scaleworkspace/covid19/Ventilator_Assembly/Plug.stl

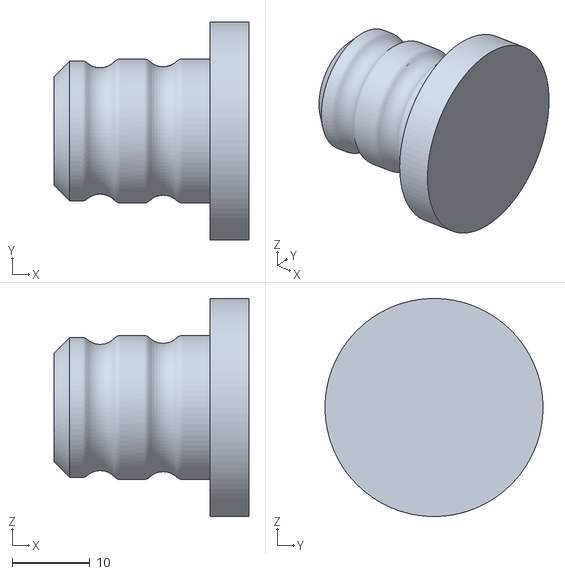
[picture p16: CAD file, 2020-03-19]
Ventilator_Assembly/Plug.stl
25.0 x 28.0 x 28.0
