scaleworkspace/covid19/Ventilator_SinglePart/Pipe Connector.STL

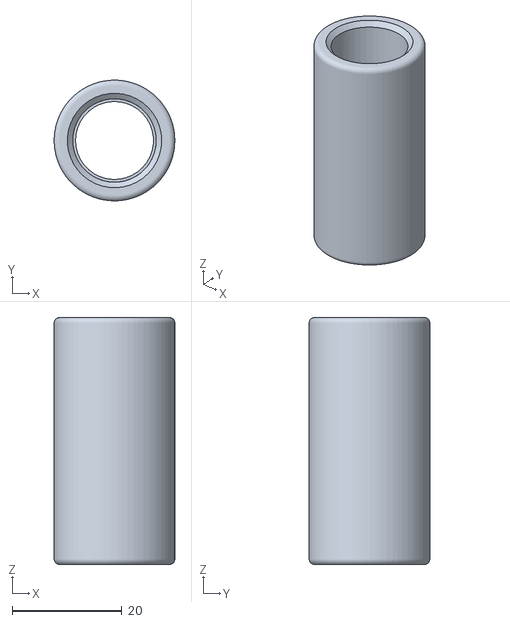
[picture p17: CAD file, 2020-03-19]
Ventilator_SinglePart/Pipe Connector.STL
22.0 x 22.0 x 45.0
