scaleworkspace/covid19/Disposable Mask/Disposable Mask V2/Disposable Mask.dxf

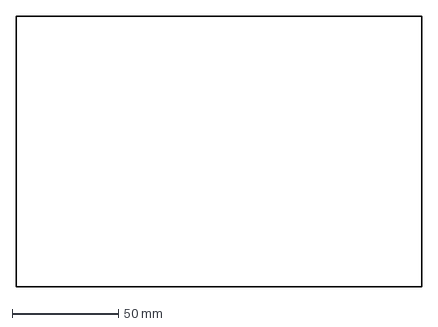
[picture p18: CAD file, 2020-03-19]
Disposable Mask/Disposable Mask V2/Disposable Mask.dxf
190.5 x 127.0 mm
