scaleworkspace/covid19/Face Shield/Face Shield V4/Face Shield (Shield) V4 Master.dxf

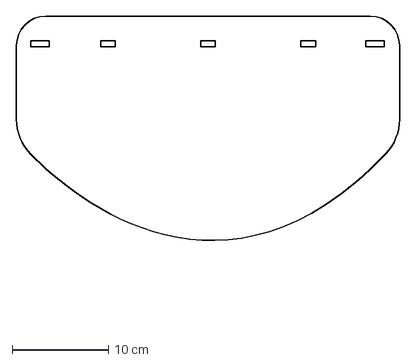
[picture p19: CAD file, 2020-03-19]
Face Shield/Face Shield V4/Face Shield (Shield) V4 Master.dxf
39.8 x 31.8 cm
