scaleworkspace/covid19/Face Shield/FullFaceShield_V3/Front Pad Print.stl

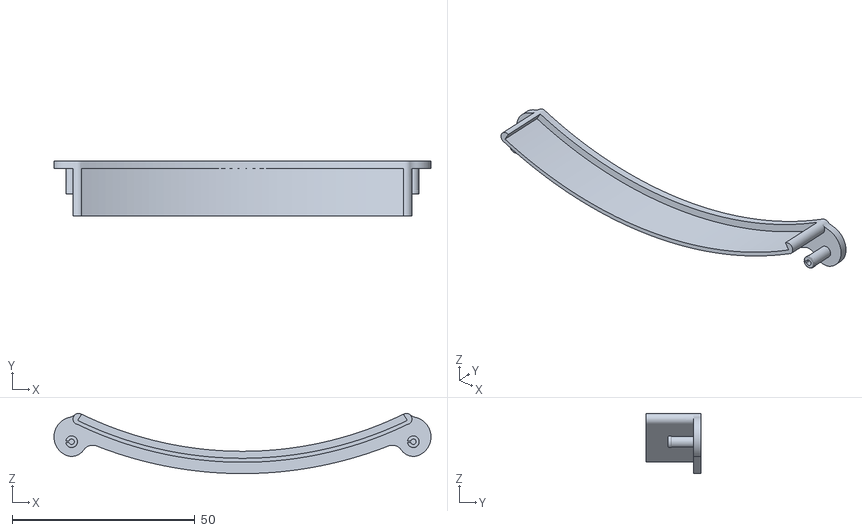
[picture p20: CAD file, 2020-03-18]
Face Shield/FullFaceShield_V3/Front Pad Print.stl
103.1 x 15.0 x 16.5
