scaleworkspace/covid19/Ventilator_Assembly/MiddleVent.stl

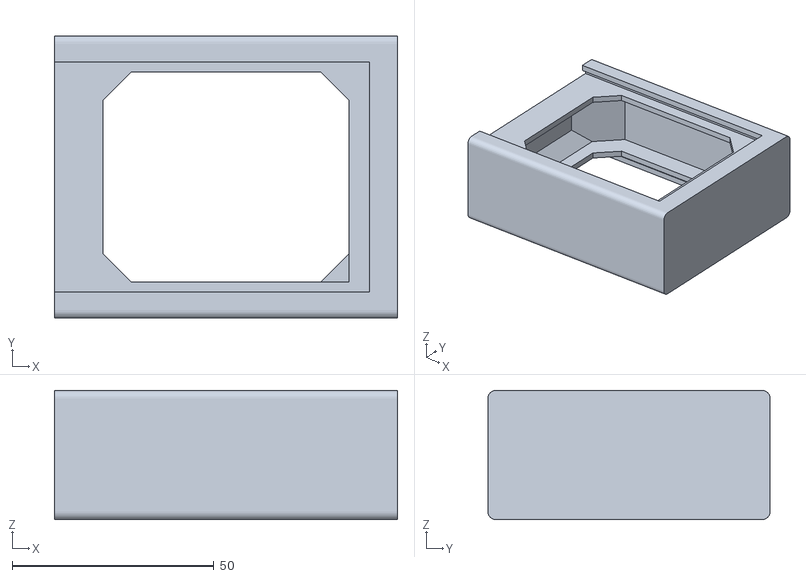
[picture p21: CAD file, 2020-03-19]
Ventilator_Assembly/MiddleVent.stl
85.0 x 70.0 x 32.0
