scaleworkspace/covid19/Ventilator_SinglePart/Cap.STL

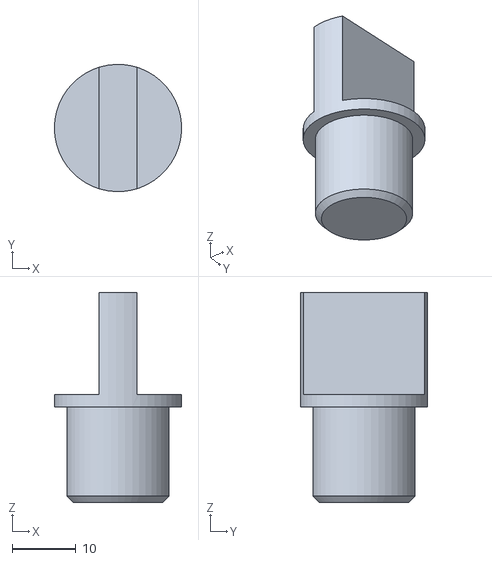
[picture p22: CAD file, 2020-03-19]
Ventilator_SinglePart/Cap.STL
20.0 x 20.0 x 33.0
