scaleworkspace/covid19/Face Shield/FullFaceShield_V3/Left Pad Print.stl

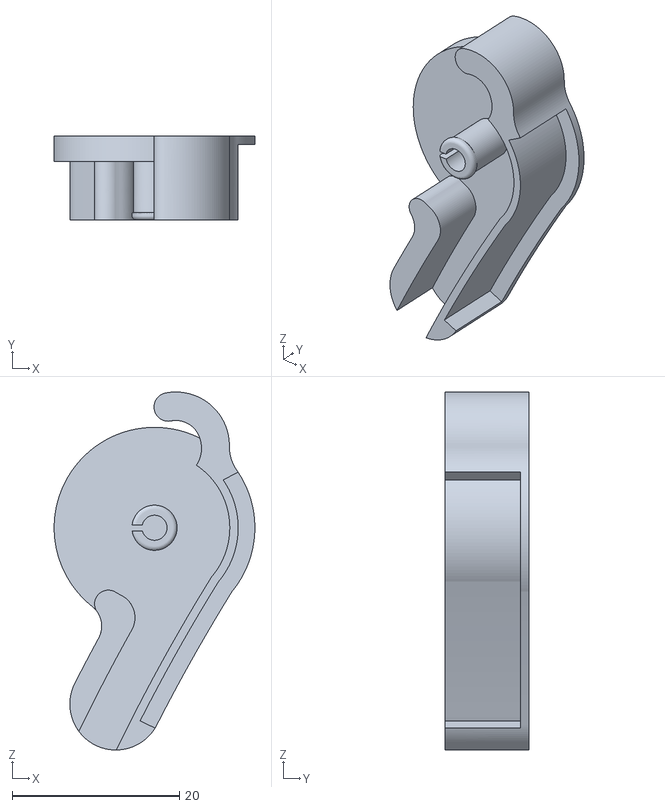
[picture p23: CAD file, 2020-03-18]
Face Shield/FullFaceShield_V3/Left Pad Print.stl
24.0 x 10.00 x 42.8
