scaleworkspace/covid19/Ventilator_Assembly/BottomTube.stl

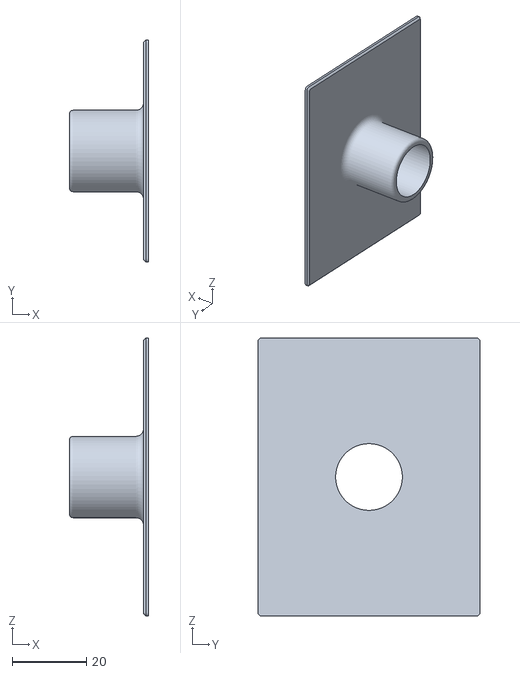
[picture p24: CAD file, 2020-03-19]
Ventilator_Assembly/BottomTube.stl
21.4 x 60.0 x 75.0
